CE-GPP/Family_Board/Unity/Family Board Virtual Device/Assets/Plugins/CW/LeanCommon/Examples/Textures/Plus.png

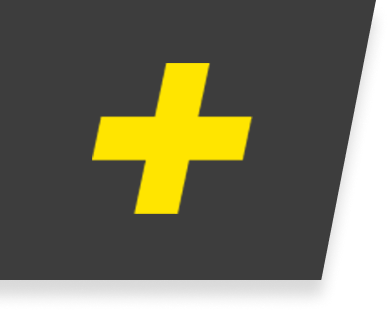
Unity/Family Board Virtual Device/Assets/Plugins/CW/LeanCommon/Examples/Textures/Plus.png
