CE-GPP/Family_Board/Unity/Family Board Virtual Device/Assets/Plugins/CW/LeanTouch/Examples/Textures/GlowingDot.png

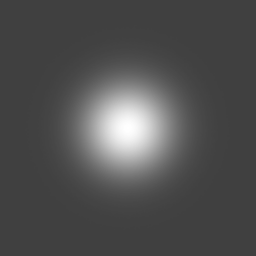
Unity/Family Board Virtual Device/Assets/Plugins/CW/LeanTouch/Examples/Textures/GlowingDot.png
