CE-GPP/Family_Board/Unity/Family Board Virtual Device/Assets/Plugins/CW/Shared/Common/Examples/Textures/DemoDescription.png

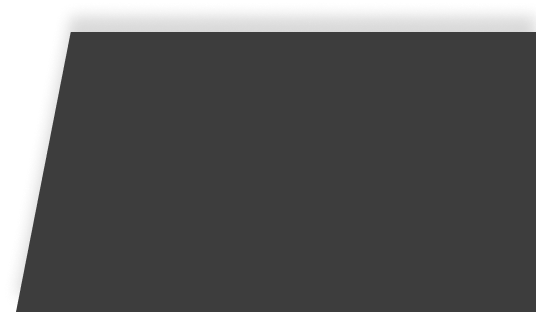
Unity/Family Board Virtual Device/Assets/Plugins/CW/Shared/Common/Examples/Textures/DemoDescription.png
