CE-GPP/Family_Board/Unity/Family Board Virtual Device/Assets/Prefab/162-lcd-display/textures/LCD1602-Parallel-LCD-Display-Yellow-Backlight-ROBU_1.png

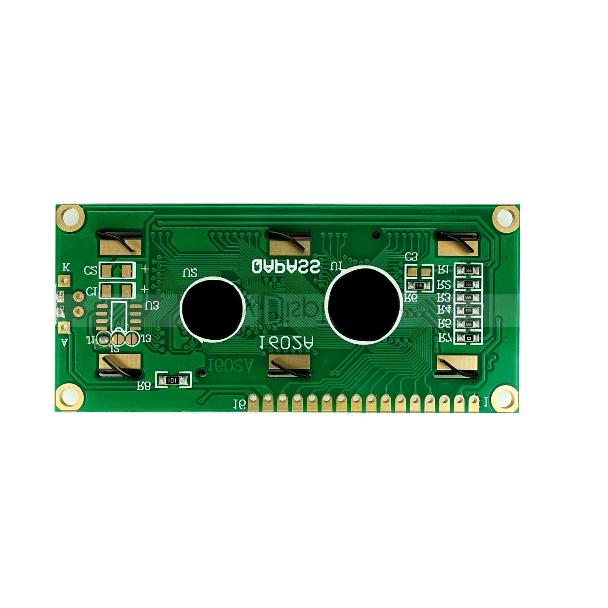
Unity/Family Board Virtual Device/Assets/Prefab/162-lcd-display/textures/LCD1602-Parallel-LCD-Display-Yellow-Backlight-ROBU_1.png
