CE-GPP/Family_Board/Unity/Family Board Virtual Device/Assets/Prefab/162-lcd-display/textures/lcd-display-500x500_0.png

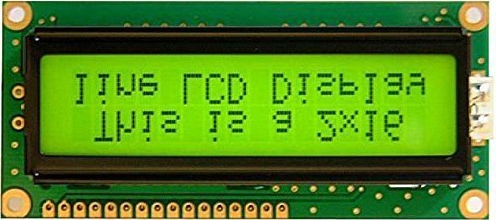
Unity/Family Board Virtual Device/Assets/Prefab/162-lcd-display/textures/lcd-display-500x500_0.png
