CE-GPP/Family_Board/Unity/Family Board Virtual Device/Assets/Prefab/Father.jpg

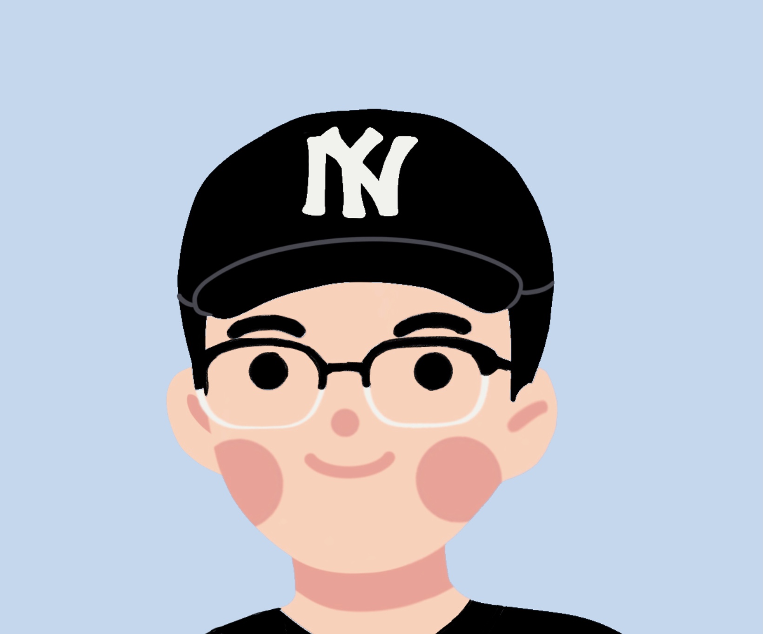
Unity/Family Board Virtual Device/Assets/Prefab/Father.jpg
