CE-GPP/Family_Board/Unity/Family Board Virtual Device/Assets/Prefab/Mother.jpg

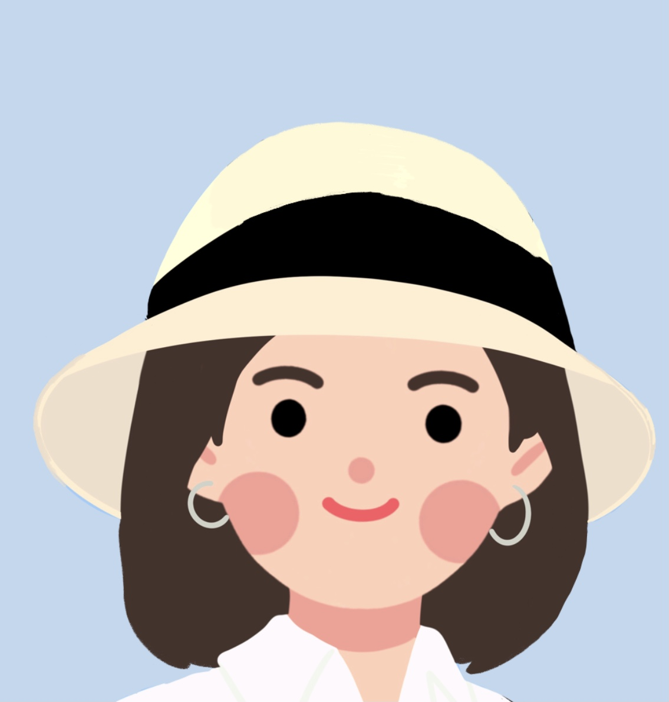
Unity/Family Board Virtual Device/Assets/Prefab/Mother.jpg
