CE-GPP/Family_Board/Unity/Family Board Virtual Device/Assets/Prefab/Son.jpg

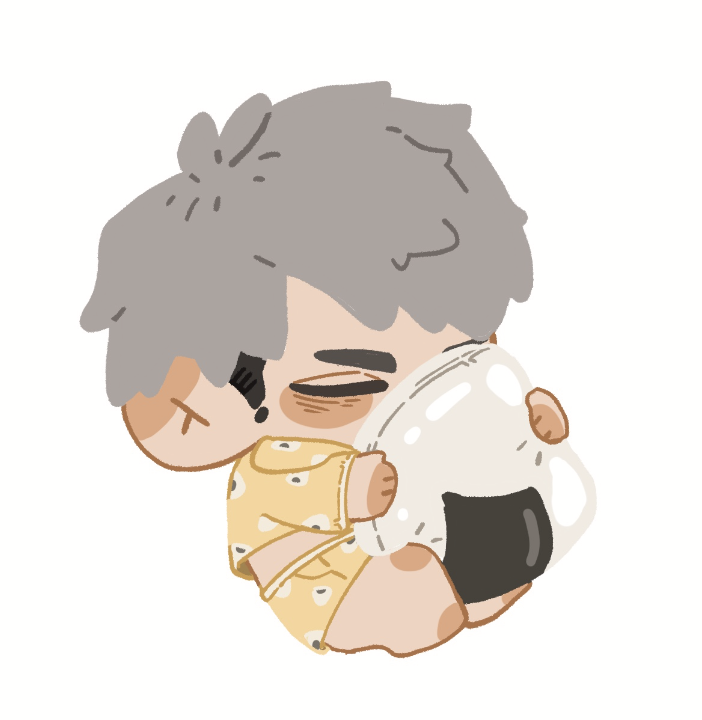
Unity/Family Board Virtual Device/Assets/Prefab/Son.jpg
