CE-GPP/Family_Board/Unity/Family Board Virtual Device/Assets/ExampleAssets/Tutorial/Images/1-welcome-screen-image.png

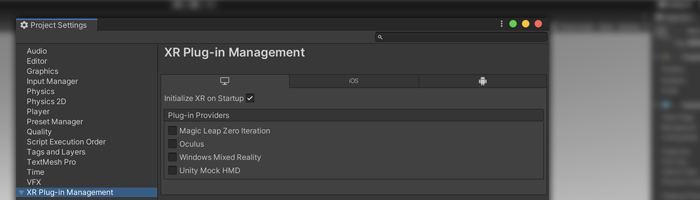
Unity/Family Board Virtual Device/Assets/ExampleAssets/Tutorial/Images/1-welcome-screen-image.png
