CE-GPP/Family_Board/Unity/Family Board Virtual Device/Assets/ExampleAssets/Tutorial/Images/project-header-ar.png

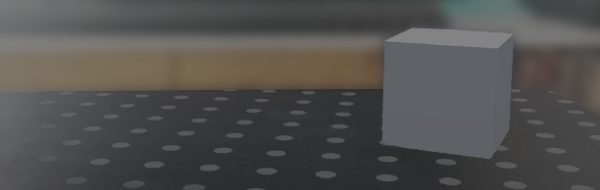
Unity/Family Board Virtual Device/Assets/ExampleAssets/Tutorial/Images/project-header-ar.png
