CE-GPP/Family_Board/Unity/Family Board Virtual Device/Assets/Model/Materials/TexturesCom_PrintedConcrete_1K/TexturesCom_PrintedConcrete_1K_albedo.tif

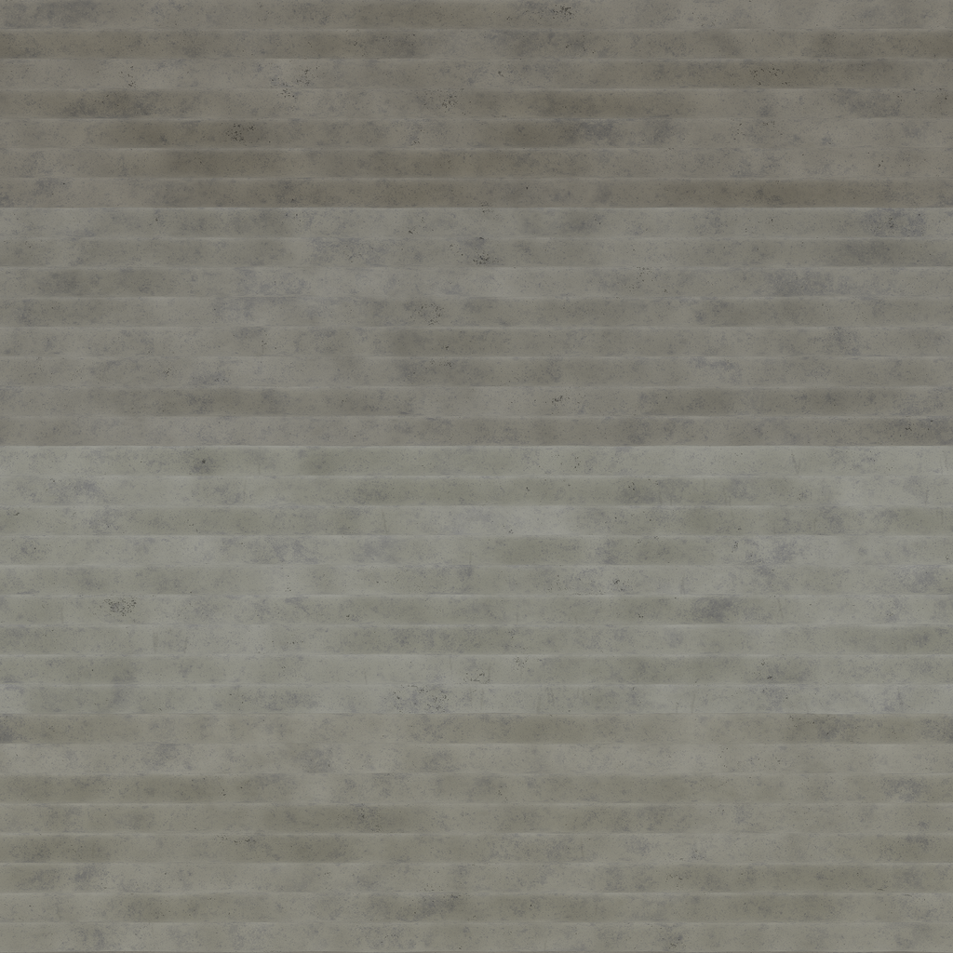
Unity/Family Board Virtual Device/Assets/Model/Materials/TexturesCom_PrintedConcrete_1K/TexturesCom_PrintedConcrete_1K_albedo.tif
