CE-GPP/Family_Board/Unity/Family Board Virtual Device/Assets/Model/Materials/TexturesCom_PrintedConcrete_1K/TexturesCom_PrintedConcrete_1K_roughness.tif

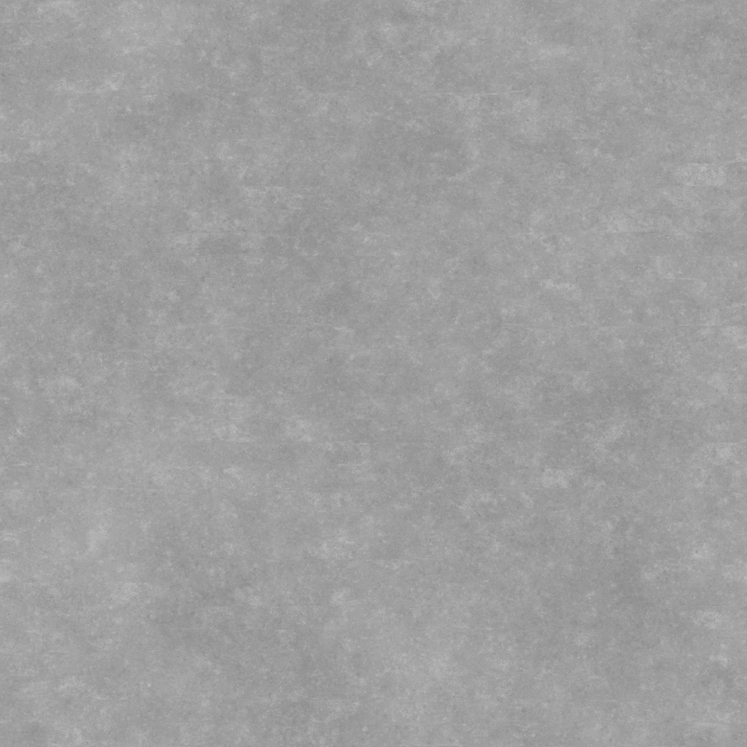
Unity/Family Board Virtual Device/Assets/Model/Materials/TexturesCom_PrintedConcrete_1K/TexturesCom_PrintedConcrete_1K_roughness.tif
